markusgruen/DccFunctionDecoder/Software/DccFunctionDecoder_4ch/CV_default_values.h

#ifndef CV_DEFAULT_VALUES_H
#define CV_DEFAULT_VALUES_H

#pragma once
#include <Arduino.h>


struct CVDefaults {
  uint8_t address;  // CV-Number (CV1 = 1, CV29 = 29, etc.)
  uint8_t value;    // value of CV
};

extern const CVDefaults defaultCVs[];
extern const uint8_t numDefaultCVs;

#endif
